UPD2DMX/UDP2DMX-ESP32/Hardware/esp32-udp2dmx.kicad_sch

## KiCad design Hardware/esp32-udp2dmx.kicad_sch (2025-08-19)

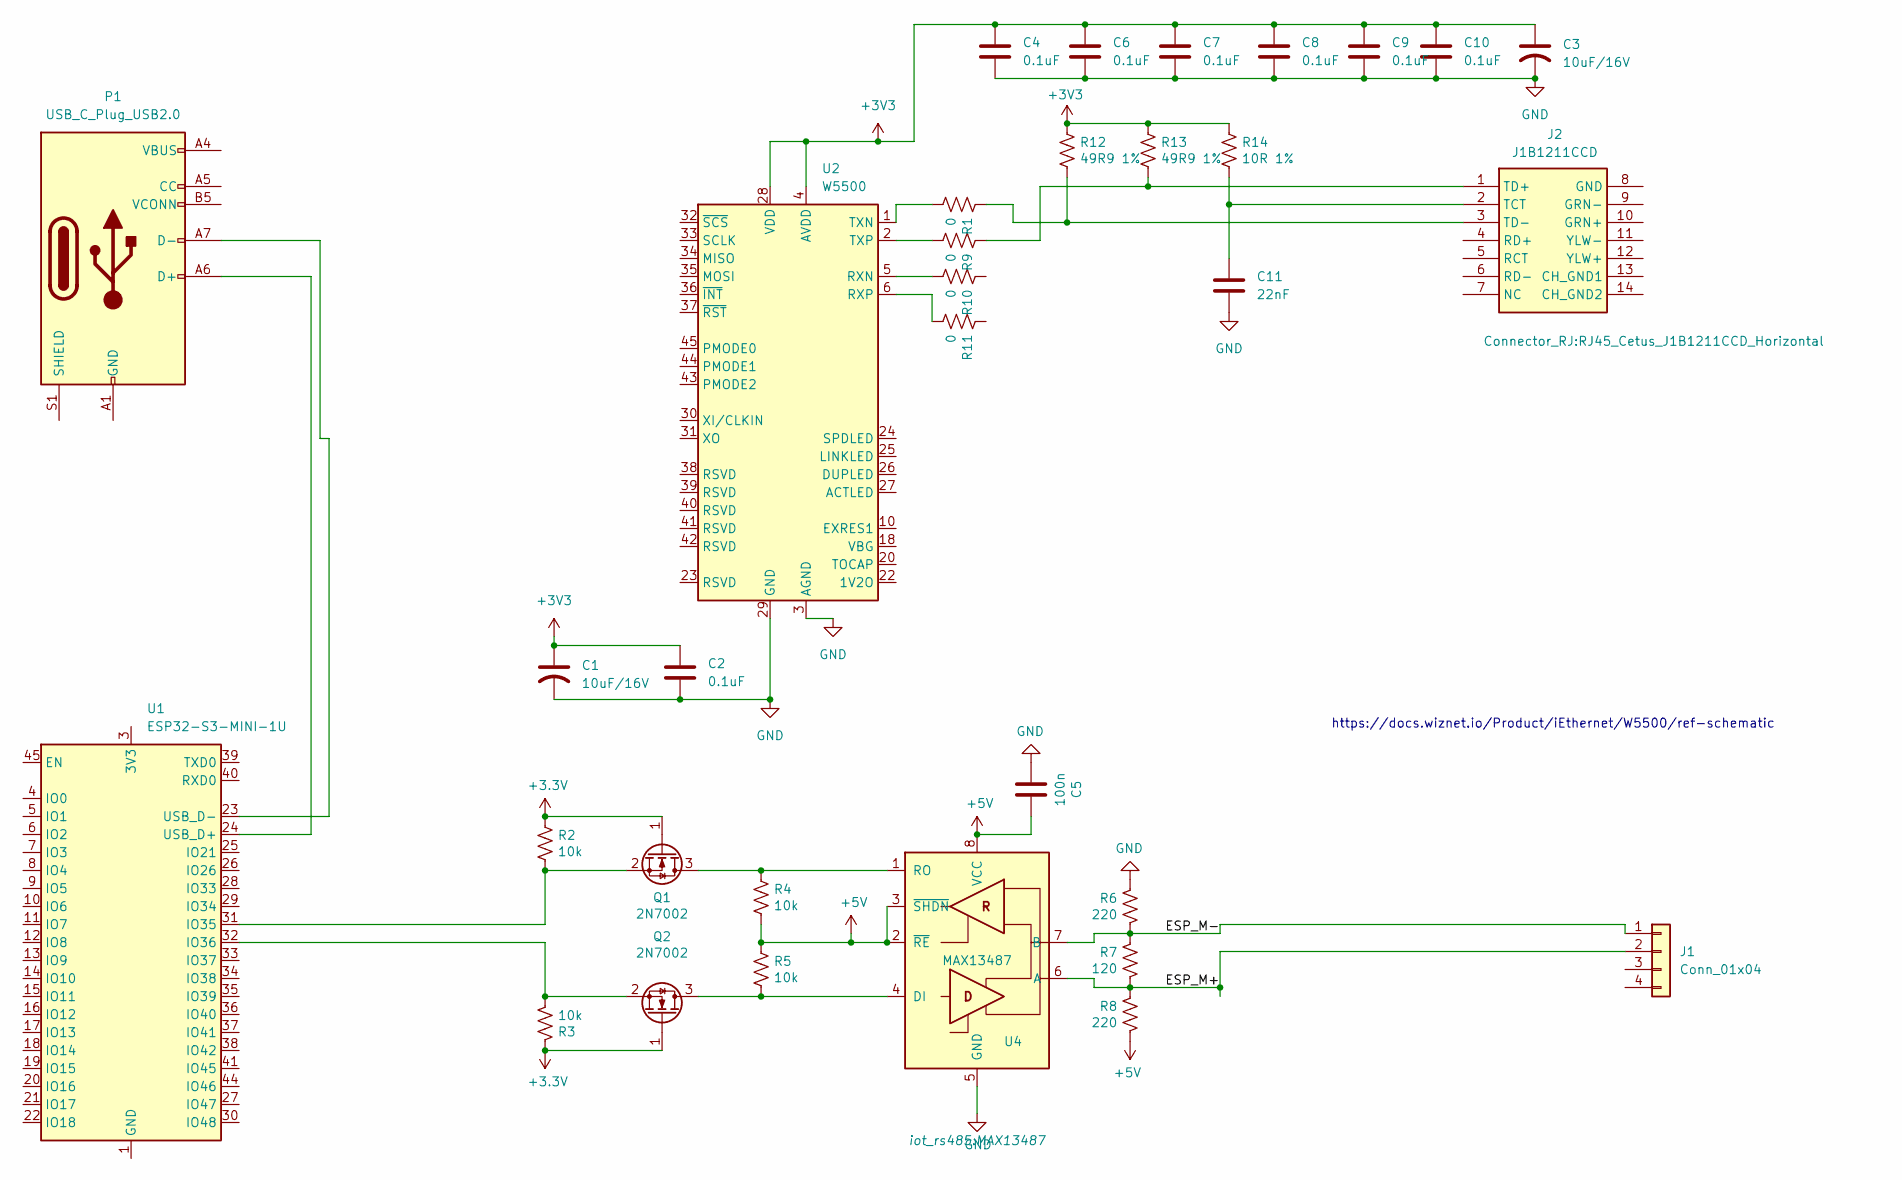
[picture p2: schematic esp32-udp2dmx.kicad_sch]

Parts:
C1, C3: 10uF/16V; C_0201_0603Metric
C2, C4, C6, C7, C8, C9, C10: 0.1uF; C_0201_0603Metric
C5: 100n; C_0603_1608Metric
C11: 22nF; C_0201_0603Metric
J1: Conn_01x04
J2: J1B1211CCD; RJ45_Cetus_J1B1211CCD_Horizontal; Mouser Part Number 950-J1B1211CCD
P1: USB_C_Plug_USB2.0
Q1, Q2: 2N7002; SOT-23
R1, R9, R10, R11: 0; R_0603_1608Metric
R2, R3, R4, R5: 10k; R_0603_1608Metric
R6, R8: 220; R_0603_1608Metric
R7: 120; R_0603_1608Metric
R12, R13: 49R9 1%; R_0603_1608Metric
R14: 10R 1%; R_0603_1608Metric
U1: ESP32-S3-MINI-1U; ESP32-S2-MINI-1U
U2: W5500; LQFP-48_7x7mm_P0.5mm
U4: MAX13487

Connections:
+3.3V: Q1.1 (G), Q2.1 (G), R2.1, R3.1
+3V3: C1.1, C2.1, C3.1, C4.1, C6.1, C7.1, C8.1, C9.1, C10.1, R12.1, R13.1, R14.1, U2.4 (AVDD), U2.8 (AVDD), U2.11 (AVDD), U2.15 (AVDD), U2.17 (AVDD), U2.21 (AVDD), U2.28 (VDD)
+5V: C5.1, R4.2, R5.1, R8.1, U4.2 (~RE), U4.3 (~SHDN), U4.8 (VCC)
ESP_M+: J1.2, R7.1, R8.2, U4.6 (A)
ESP_M-: J1.1, R6.1, R7.2, U4.7 (B)
GND: C1.2, C2.2, C3.2, C4.2, C5.2, C6.2, C7.2, C8.2, C9.2, C10.2, C11.2, R6.2, U2.3 (AGND), U2.9 (AGND), U2.14 (AGND), U2.16 (AGND), U2.19 (AGND), U2.29 (GND), U2.48 (AGND), U4.5 (GND)
unnamed: C11.1, J2.2 (TCT), R14.2
unnamed: J2.1 (TD+), R9.1, R13.2
unnamed: J2.3 (TD-), R1.1, R12.2
unnamed: P1.A1 (GND), P1.A12 (GND), P1.B1 (GND), P1.B12 (GND)
unnamed: P1.A4 (VBUS), P1.A9 (VBUS), P1.B4 (VBUS), P1.B9 (VBUS)
unnamed: P1.A6 (D+), U1.24 (USB_D+)
unnamed: P1.A7 (D-), U1.23 (USB_D-)
unnamed: Q1.2 (S), R2.2, U1.31 (IO35)
unnamed: Q1.3 (D), R4.1, U4.1 (RO)
unnamed: Q2.2 (S), R3.2, U1.32 (IO36)
unnamed: Q2.3 (D), R5.2, U4.4 (DI)
unnamed: R1.2, U2.1 (TXN)
unnamed: R9.2, U2.2 (TXP)
unnamed: R10.2, U2.5 (RXN)
unnamed: R11.2, U2.6 (RXP)
unnamed: U1.1 (GND), U1.2 (GND), U1.42 (GND), U1.43 (GND), U1.46 (GND), U1.47 (GND), U1.48 (GND), U1.49 (GND), U1.50 (GND), U1.51 (GND), U1.52 (GND), U1.53 (GND), U1.54 (GND), U1.55 (GND), U1.56 (GND), U1.57 (GND), U1.58 (GND), U1.59 (GND), U1.60 (GND), U1.61 (GND), U1.62 (GND), U1.63 (GND), U1.64 (GND), U1.65 (GND)

Notes on the sheet:
https://docs.wiznet.io/Product/iEthernet/W5500/ref-schematic
